AgustinSiben/EMAC-2.0/Firmware Continuo/Diagrama de Flujo medición continua.png

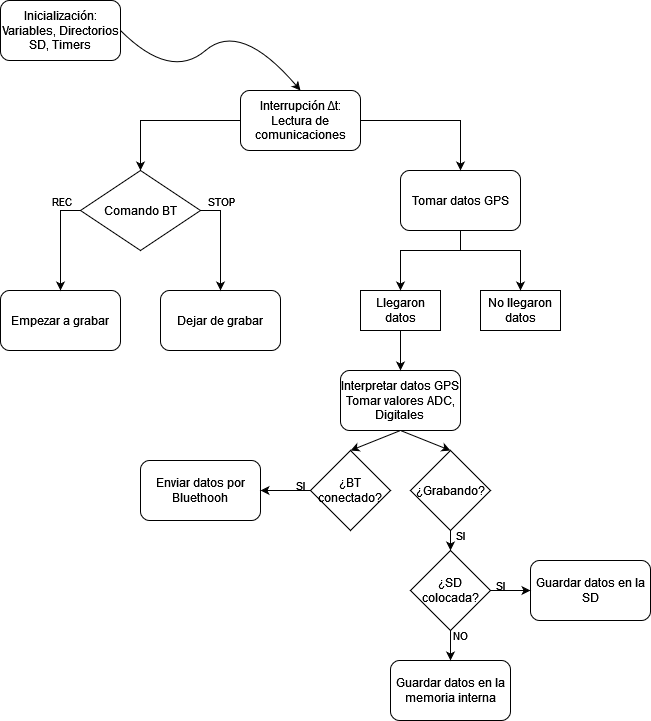
Firmware Continuo/Diagrama de Flujo medición continua.png
