AgustinSiben/EMAC-2.0/Fotos/3d1.png

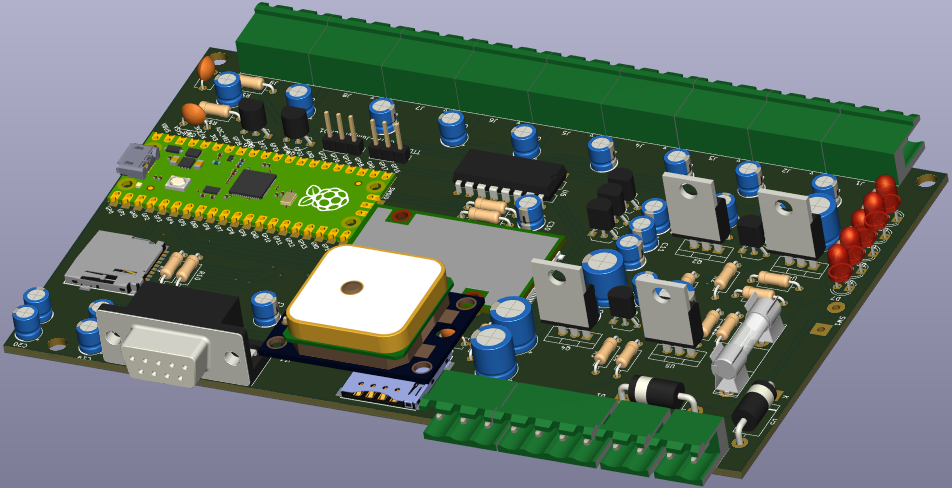
Fotos/3d1.png
