AgustinSiben/EMAC-2.0/Fotos/3d2.png

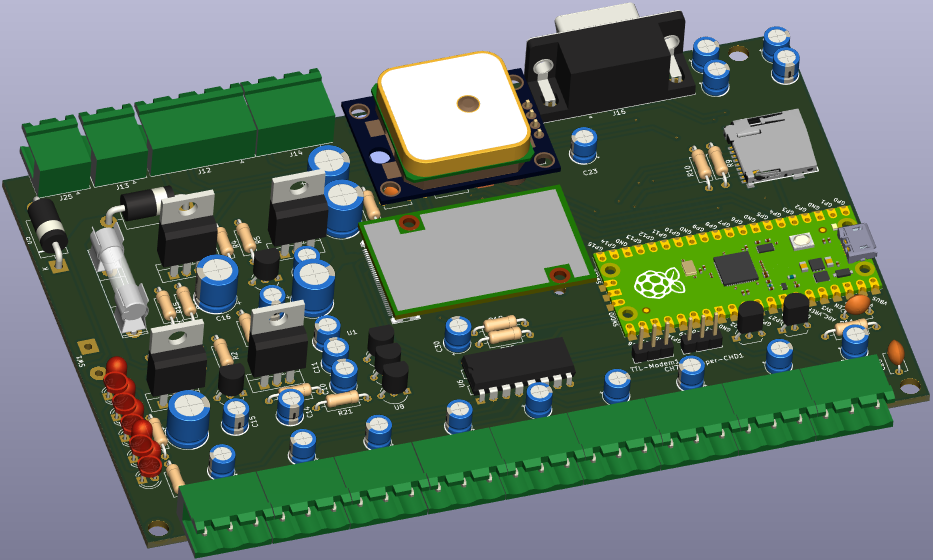
Fotos/3d2.png
