AgustinSiben/EMAC-2.0/Fotos/3d.png

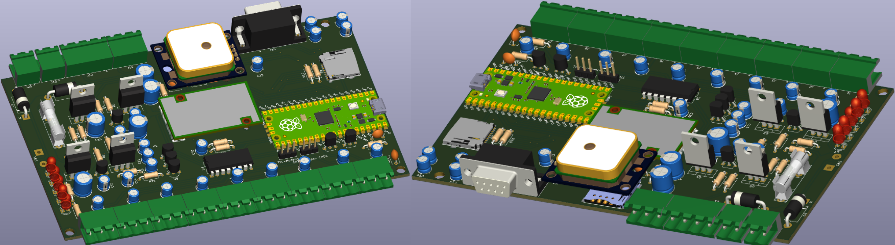
Fotos/3d.png
