AgustinSiben/EMAC-2.0/Fotos/20220310_103719.jpg

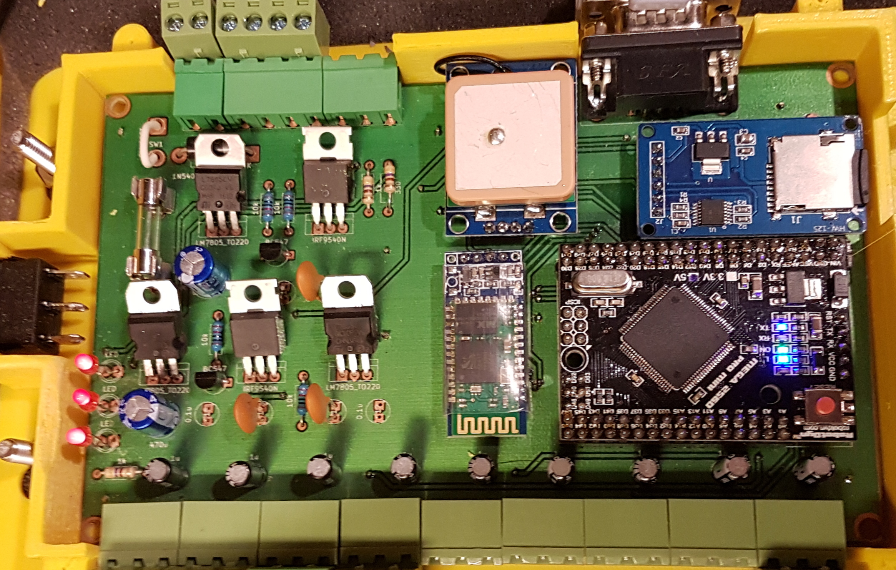
Fotos/20220310_103719.jpg
