AgustinSiben/EMAC-2.0/Fotos/Amdos DL.png

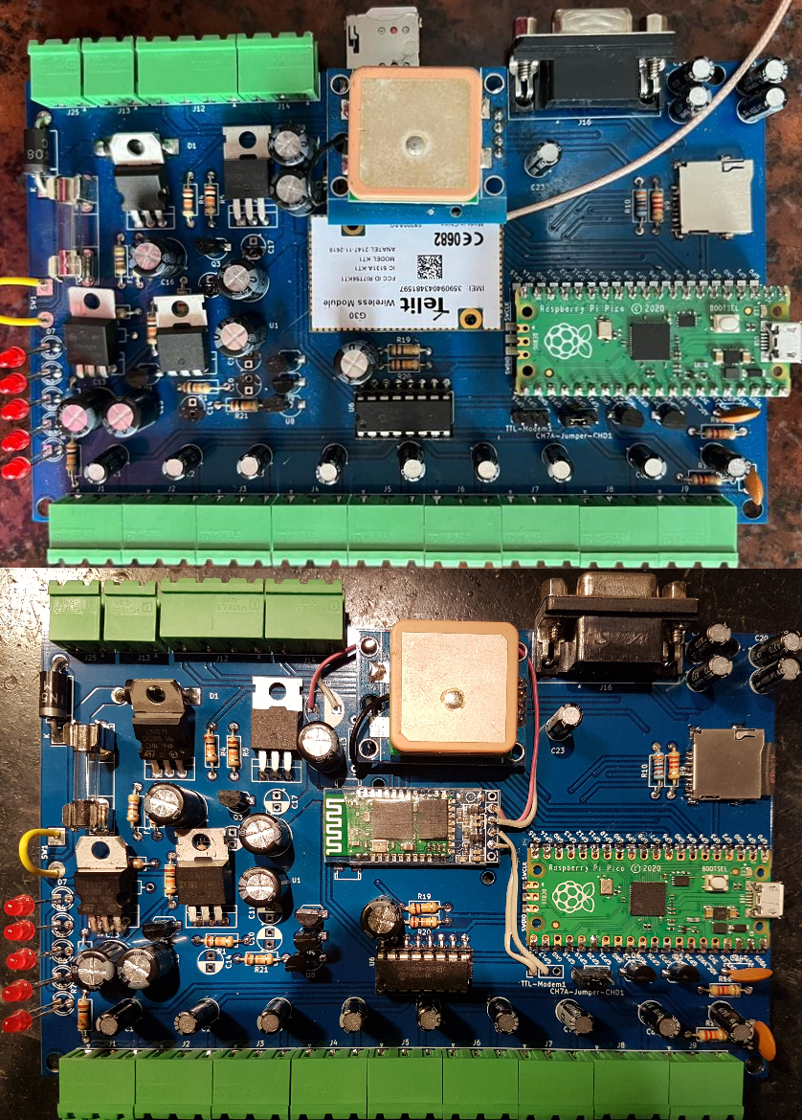
Fotos/Amdos DL.png
