AgustinSiben/EMAC-2.0/Fotos/App.jpg

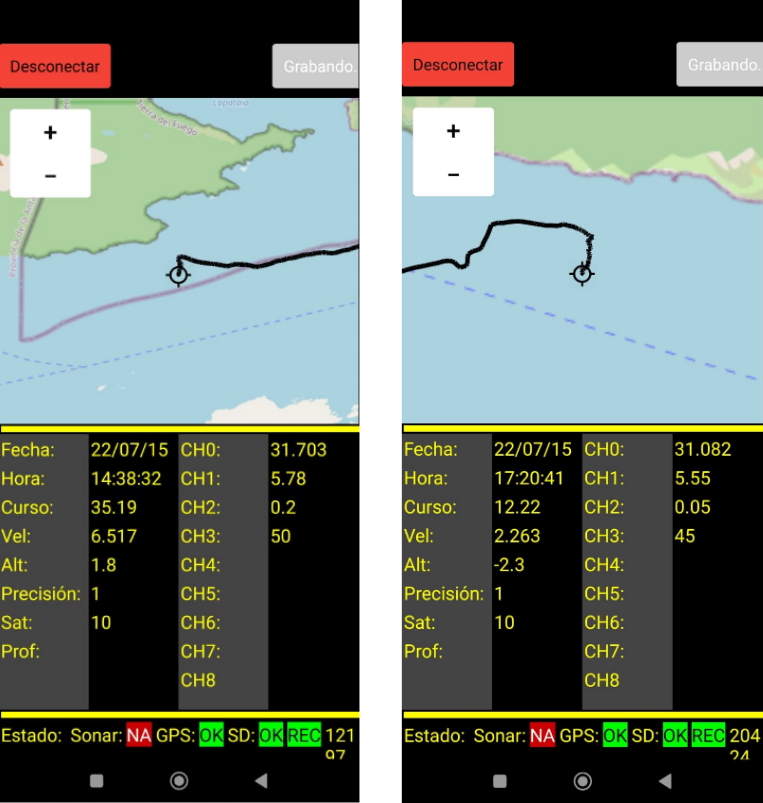
Fotos/App.jpg
