AgustinSiben/EMAC-2.0/Fotos/Autonomo.jpeg

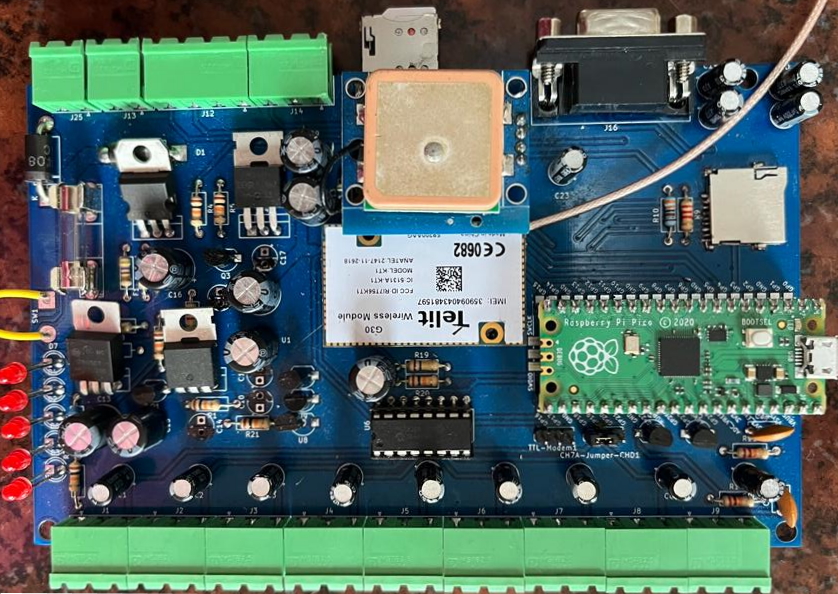
Fotos/Autonomo.jpeg
