AgustinSiben/EMAC-2.0/Fotos/Boya-Costero.jpg

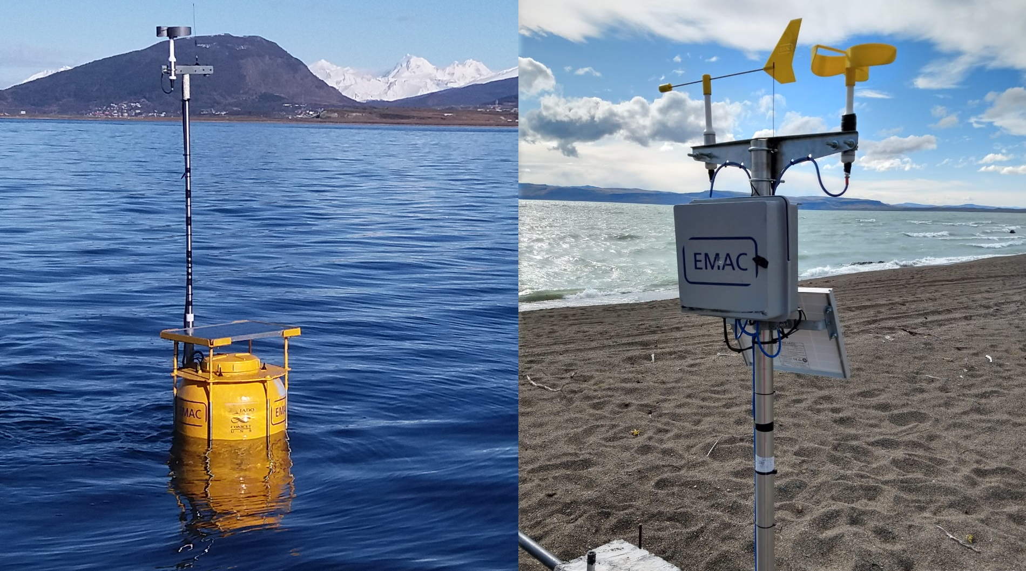
Fotos/Boya-Costero.jpg
