AgustinSiben/EMAC-2.0/Fotos/DataLogger anterior.jpeg

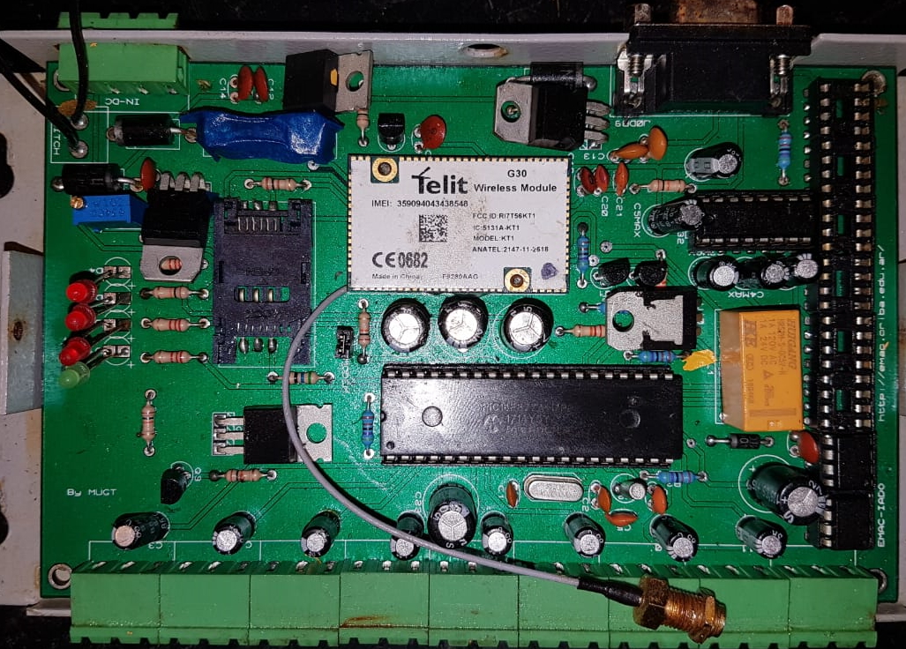
Fotos/DataLogger anterior.jpeg
