AgustinSiben/EMAC-2.0/Fotos/Datos_completo.png

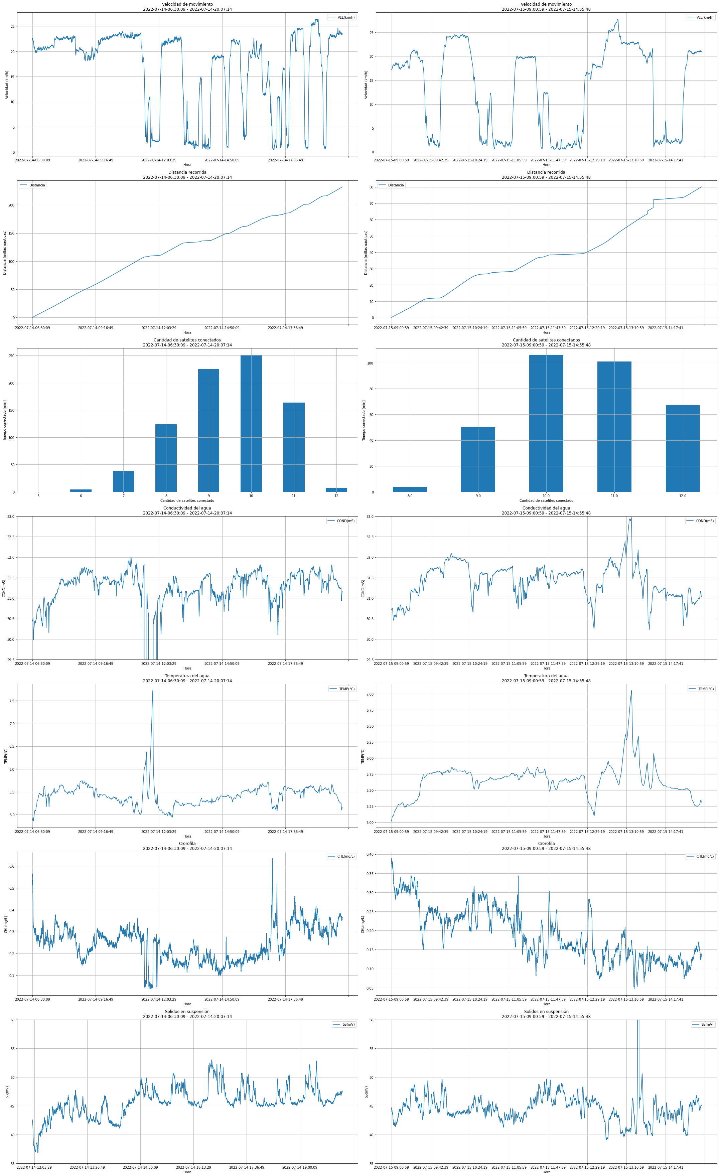
Fotos/Datos_completo.png
