AgustinSiben/EMAC-2.0/Fotos/En campo.jpg

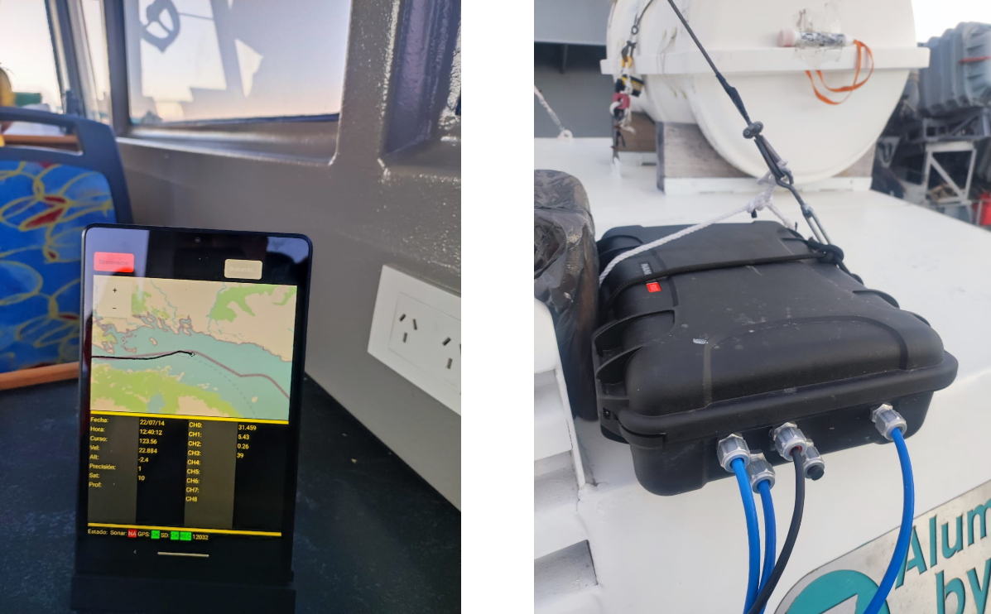
Fotos/En campo.jpg
