AgustinSiben/EMAC-2.0/Fotos/IMG-20220709-WA0050.jpg

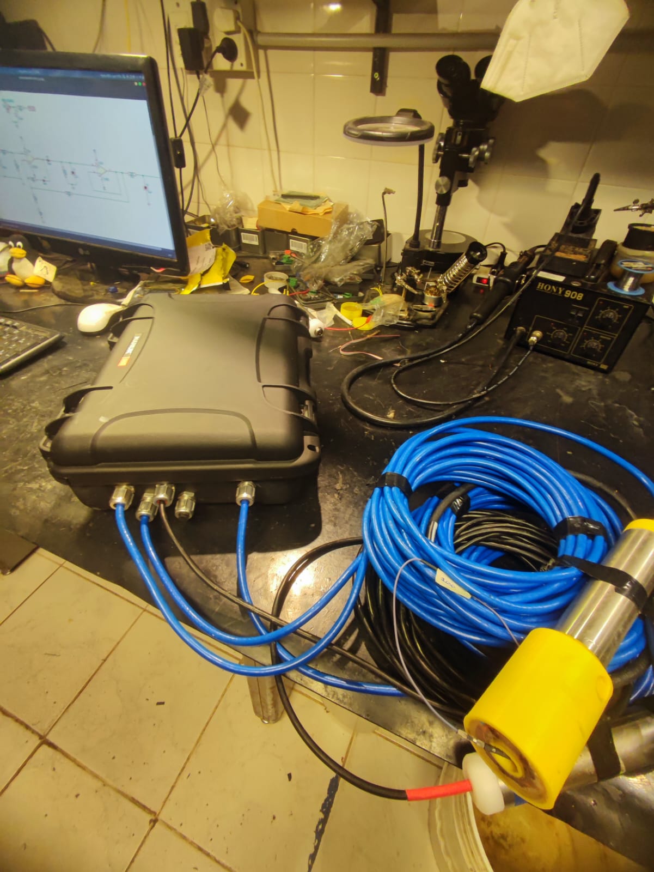
Fotos/IMG-20220709-WA0050.jpg
