AgustinSiben/EMAC-2.0/Fotos/IMG-20220726-WA0002.jpg

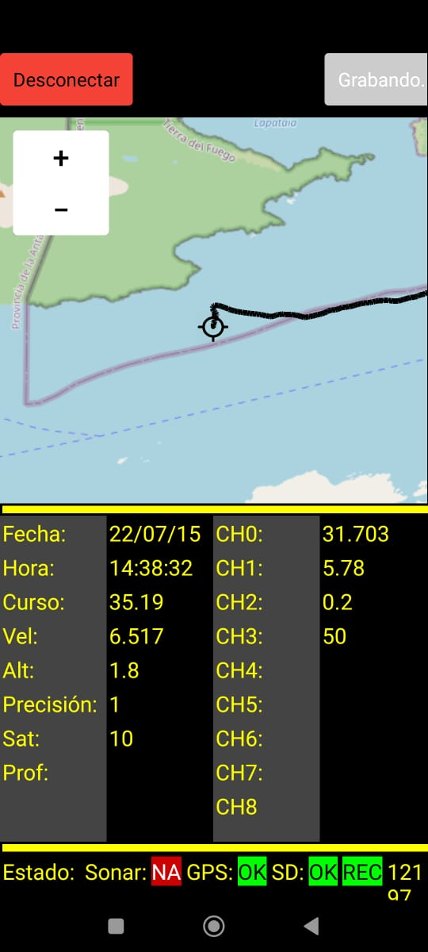
Fotos/IMG-20220726-WA0002.jpg
