AgustinSiben/EMAC-2.0/Fotos/IMG-20220726-WA0003.jpg

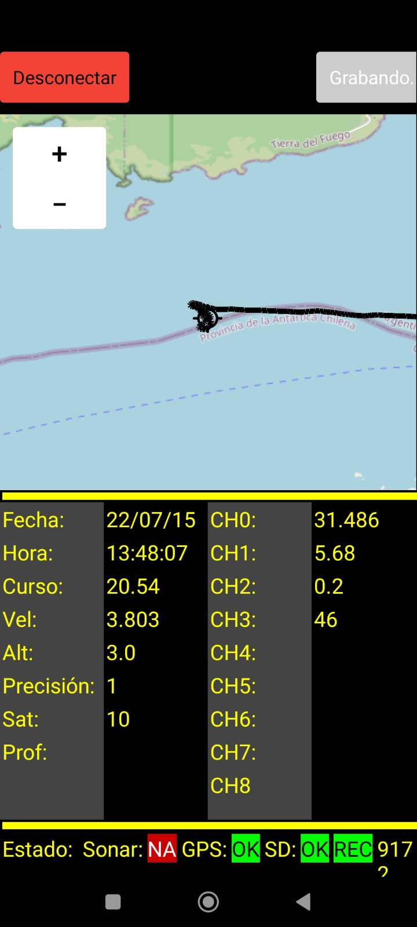
Fotos/IMG-20220726-WA0003.jpg
