AgustinSiben/EMAC-2.0/Fotos/Maletin.jpg

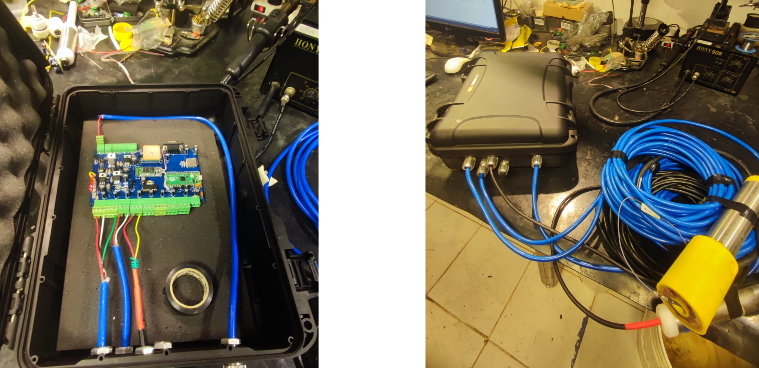
Fotos/Maletin.jpg
