AgustinSiben/EMAC-2.0/Fotos/Mapa.png

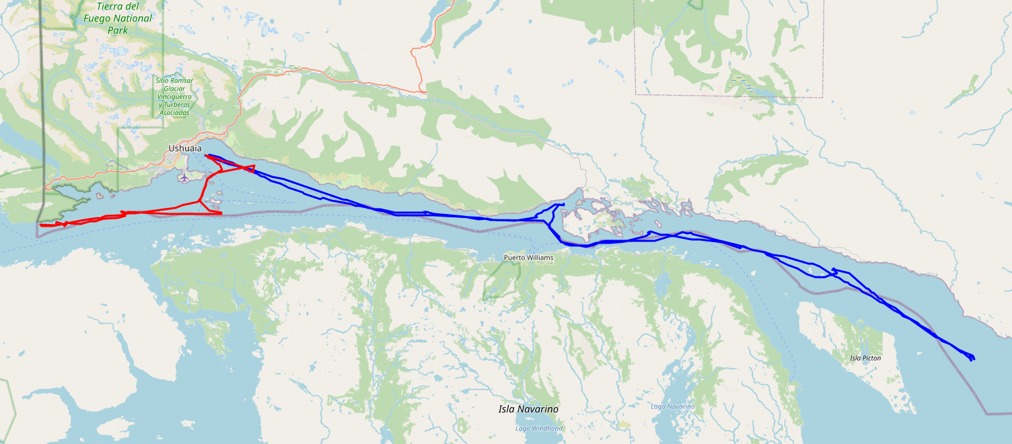
Fotos/Mapa.png
