AgustinSiben/EMAC-2.0/Fotos/PCB1.png

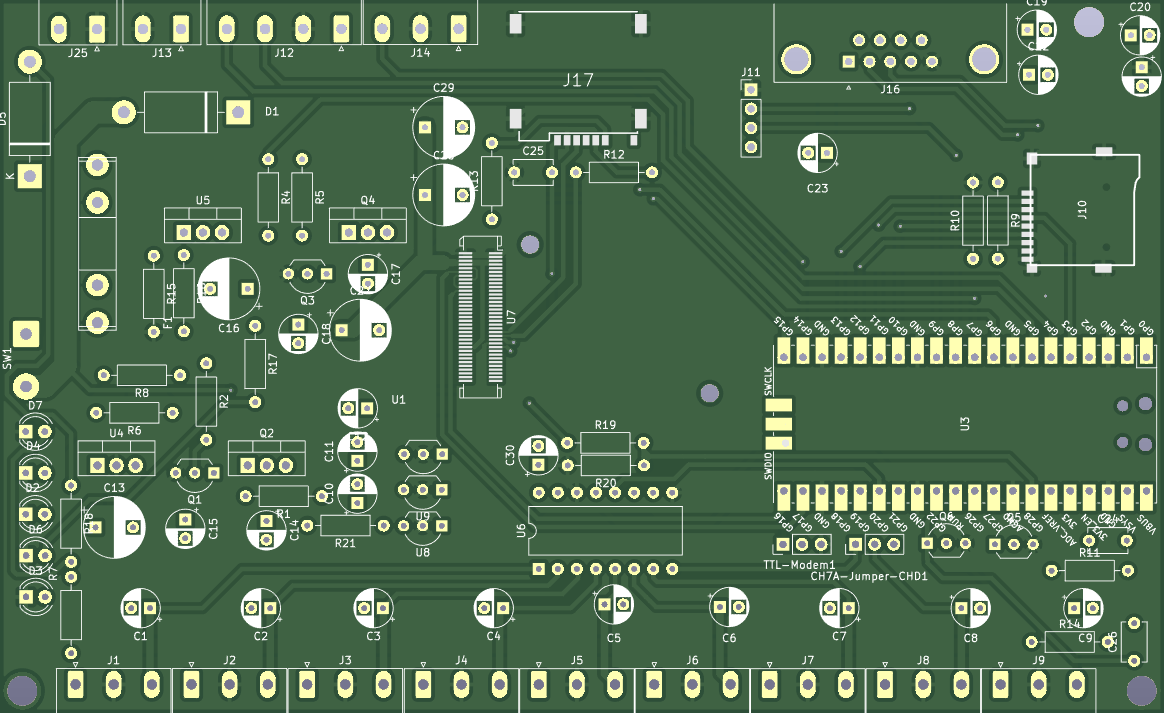
Fotos/PCB1.png
