AgustinSiben/EMAC-2.0/Fotos/PCB2.png

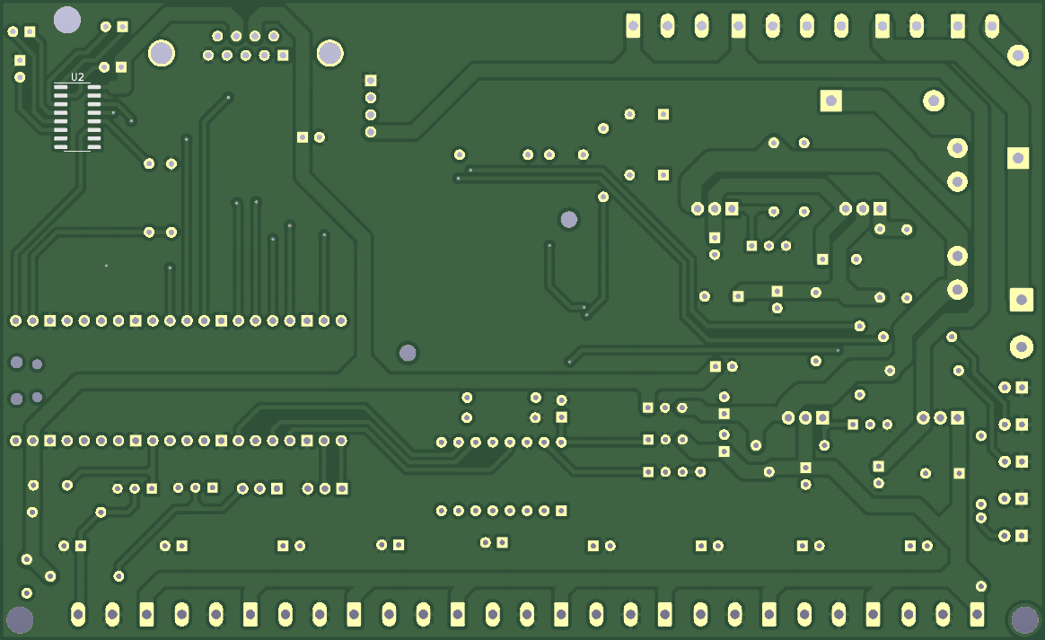
Fotos/PCB2.png
