AgustinSiben/EMAC-2.0/Fotos/PCB.png

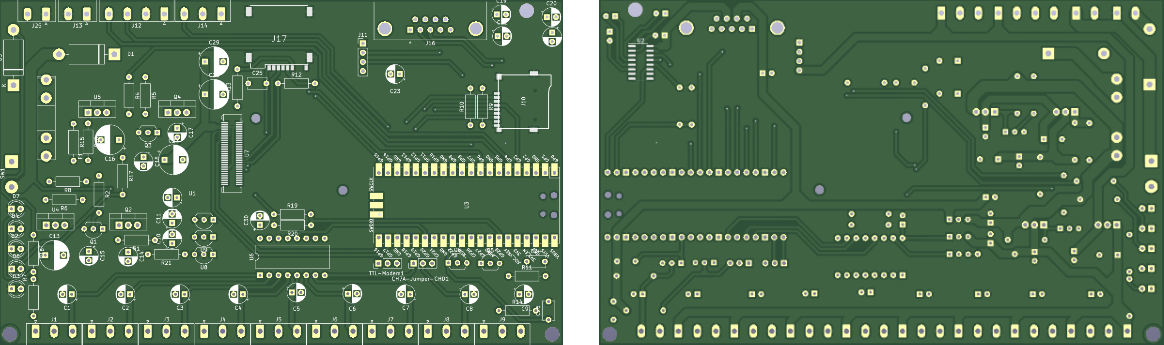
Fotos/PCB.png
