AgustinSiben/EMAC-2.0/Fotos/presentacion1.jpg

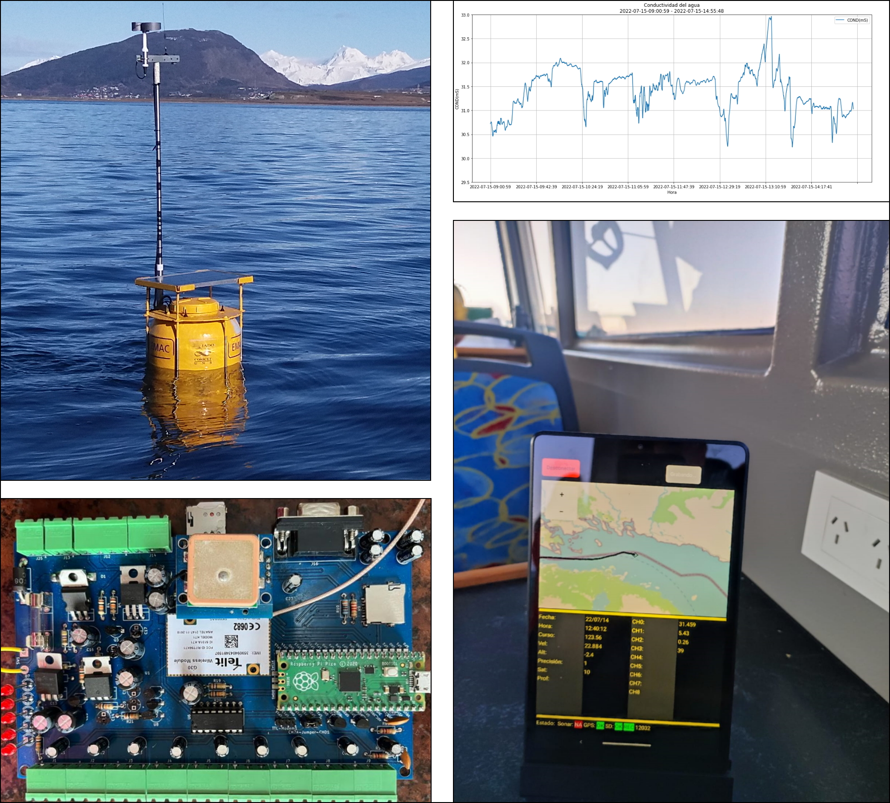
Fotos/presentacion1.jpg
