AgustinSiben/EMAC-2.0/Fotos/presentacion2.png

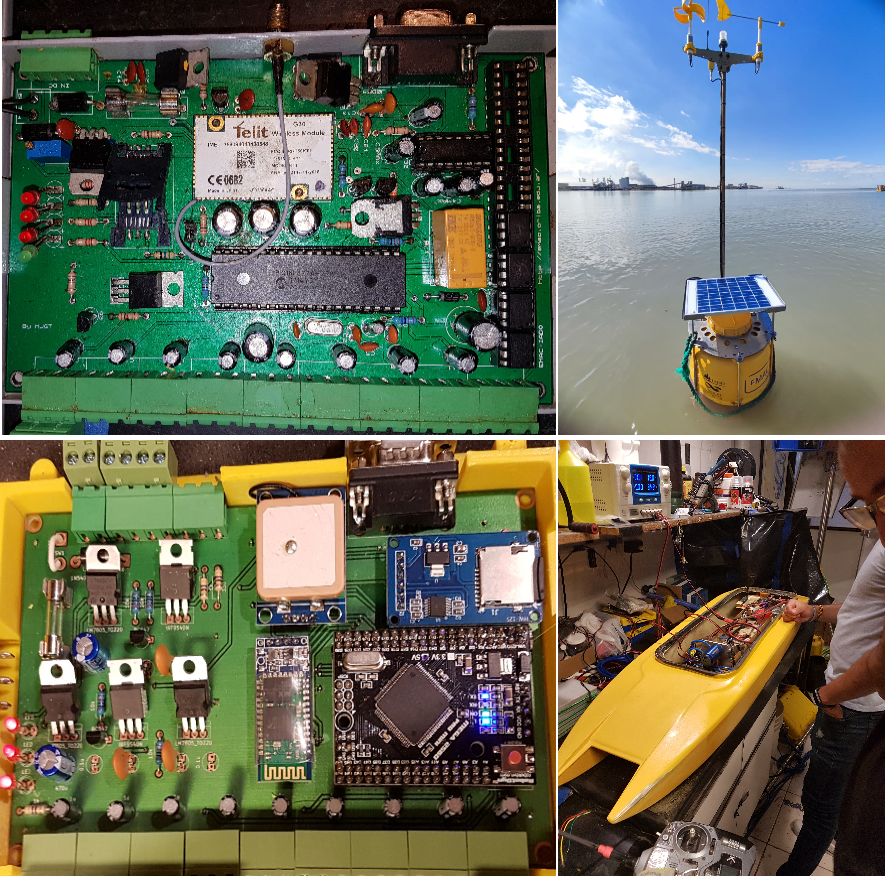
Fotos/presentacion2.png
