AgustinSiben/EMAC-2.0/Fotos/presentación3.png

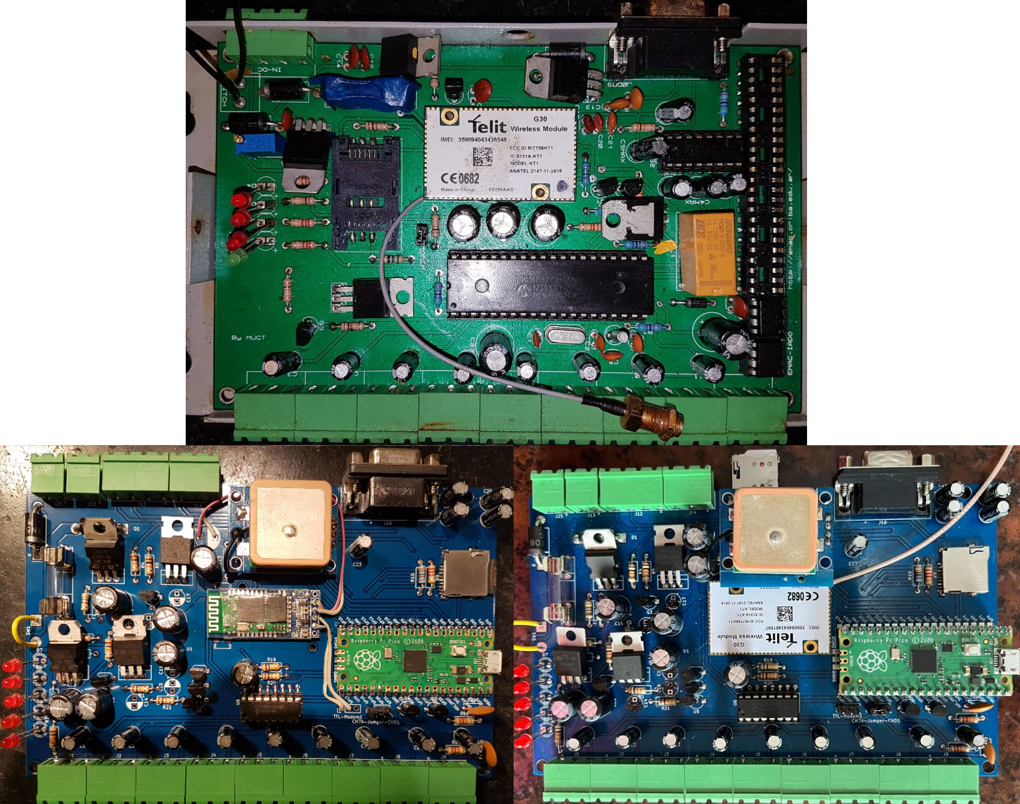
Fotos/presentación3.png
