AgustinSiben/EMAC-2.0/Fotos/WhatsApp Image 2022-08-21 at 10.00.12 AM.jpeg

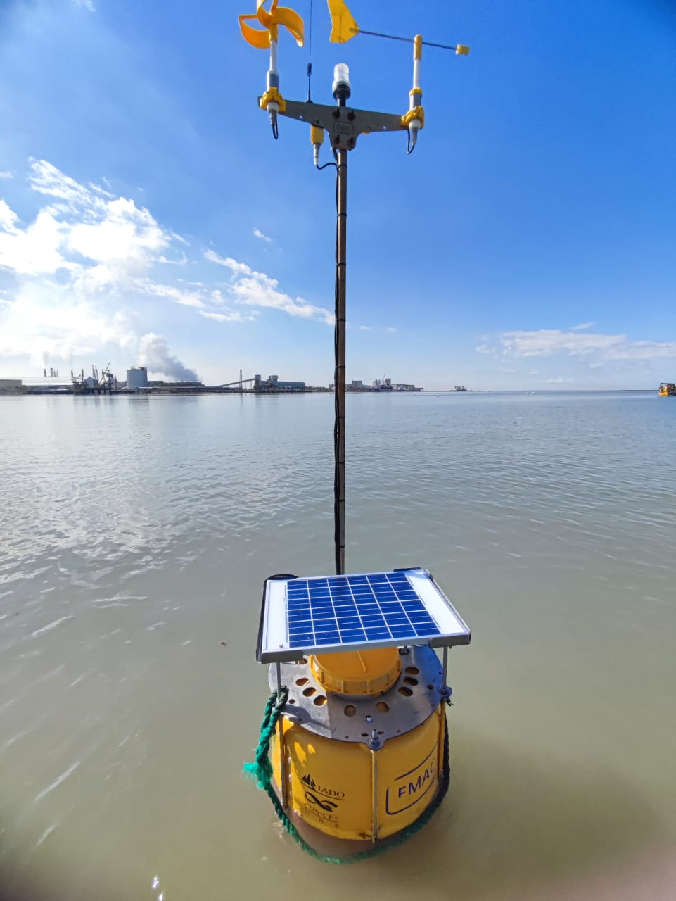
Fotos/WhatsApp Image 2022-08-21 at 10.00.12 AM.jpeg
